PetervanderBurgt/Physical_Eetlijst/Eetlijst_v5/Eetlijst_Hardware Breadboard layout.jpg

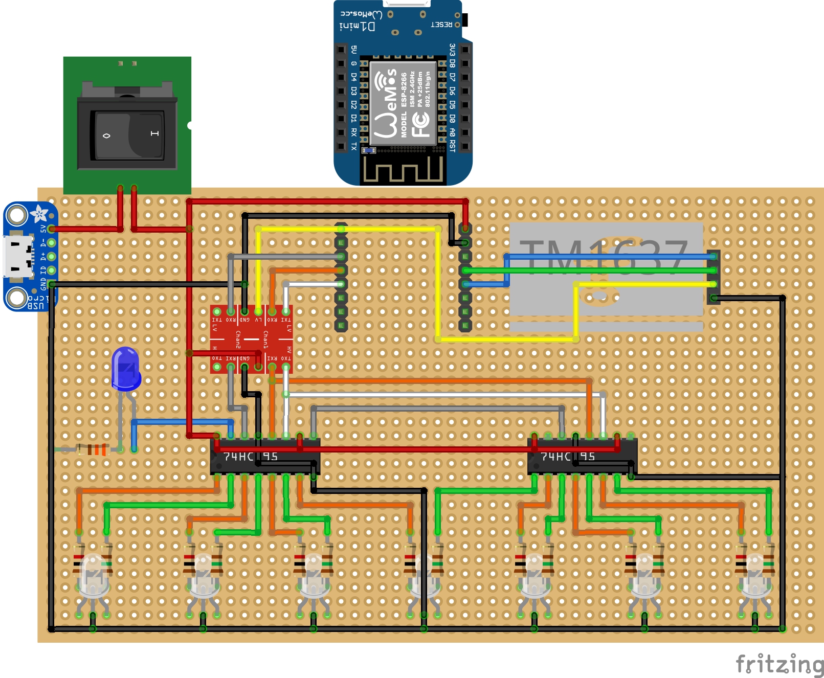
Eetlijst_v5/Eetlijst_Hardware Breadboard layout.jpg
